SzymonGogulski/POWER_SUPPLY_FOR_MOBILE_DEVICES/dokumenty/przetwornica/charts.png

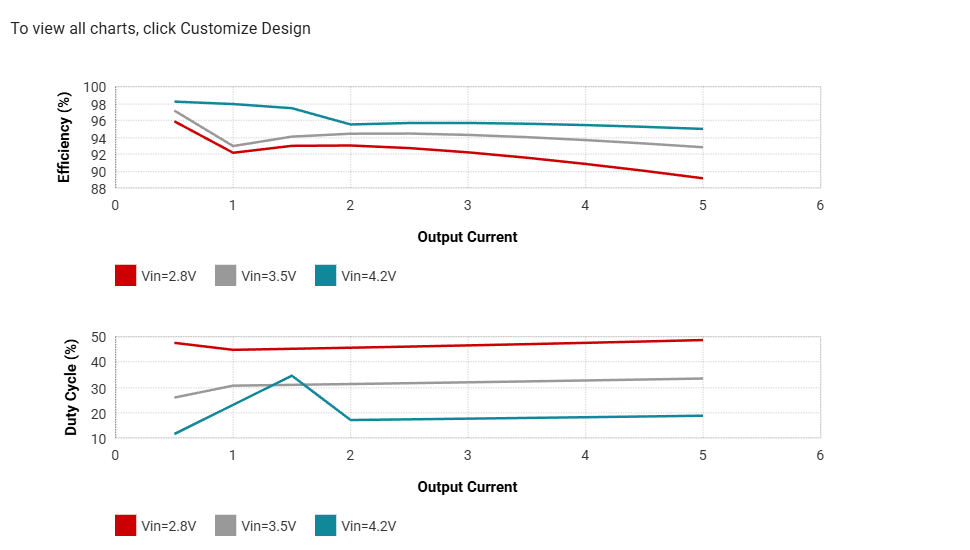
dokumenty/przetwornica/charts.png
