SzymonGogulski/POWER_SUPPLY_FOR_MOBILE_DEVICES/sprawozdanie/testy_montaz.png

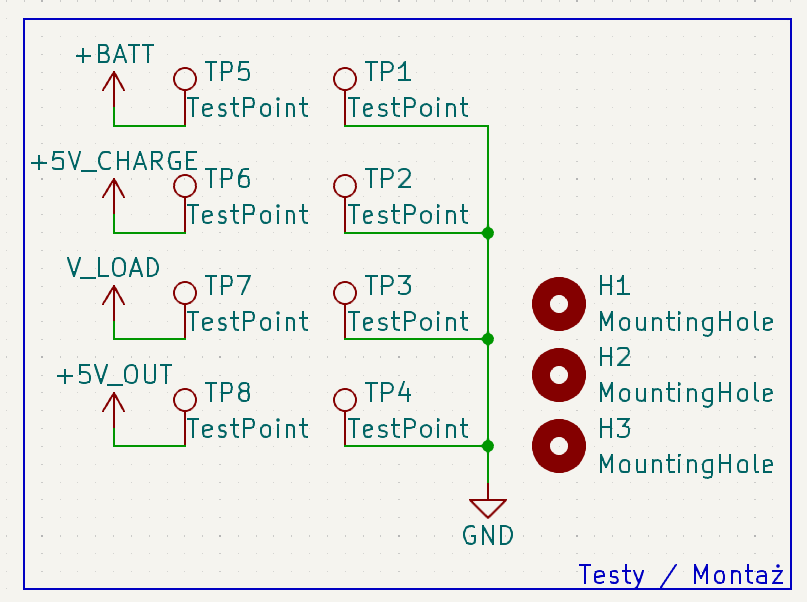
sprawozdanie/testy_montaz.png
